broedschroed/NixieClockUltra/docs/marketing/NixieClockUltra-Werbetext.odt

Nixie Clock Ultra

wenn Zeit leuchtet

Handgefertigte Röhrenuhr · ESP32-S3 · 6 × IN-12A · WiFi & Web-Interface

# Eine Uhr, die man nicht kauft, weil man die Zeit nicht kennt

Nixie-Röhren gehören zu den faszinierendsten Anzeigetechnologien, die je entwickelt wurden: warmes, leicht diffuses Licht, das Ziffern plastisch aus dem Glas herausleuchten lässt — unverwechselbar, zeitlos und heute begehrter denn je. Die Nixie Clock Ultra bringt dieses Feeling ins 21. Jahrhundert, ohne seinen Charakter zu verlieren.

Sechs IN-12A-Nixieröhren zeigen Stunden, Minuten und Sekunden — und auf Wunsch auch das Datum. Hinter jeder Röhre sitzt eine individuell ansteuerbare RGB-LED, die das Glas von innen in warmem Licht erstrahlen lässt: statisch, im sanften Atemrhythmus oder als fließendes Farbspektrum. Vier weitere LEDs beleuchten die Trennpunkte zwischen den Zifferngruppen.

Was diese Uhr von den meisten anderen Nixie-Projekten unterscheidet, ist die Art der Röhrenansteuerung: Kein Multiplexing, keine Kompromisse. Jede der 60 Kathoden besitzt ihren eigenen Hochvolt-Transistor — die Ziffern leuchten dauerhaft, ohne jegliches Ghosting oder Flimmern. Das Ergebnis ist ein sauberes, stabiles Bild, das man sofort sieht und lange nicht vergisst.

Die Uhr denkt mit: Ein ESP32-S3 verbindet sich mit dem Heimnetz, synchronisiert die Uhrzeit vollautomatisch per NTP aus dem Internet und ist über jeden Browser erreichbar — kein App-Download, kein Pairing. Über das Web-Interface lassen sich Helligkeit, Farben, Animationen, Nacht-Modus und vieles mehr bequem einstellen. Wer lieber zur Fernbedienung greift: fast jede handelsübliche IR-Fernbedienung lässt sich anlernen.

Für ruhige Nächte sorgt der Nacht-Modus: Die Uhr dimmt sich auf Wunsch zu einer konfigurierbaren Uhrzeit automatisch herunter — oder reagiert direkt auf die Umgebungshelligkeit über einen eingebauten Lichtsensor. Im Dunkelmodus erlöschen die Röhren vollständig.

Und weil eine Uhr auch eine Uhr sein soll: Die Echtzeituhr mit CR2032-Backup-Batterie hält die Zeit auch bei Stromausfall zuverlässig. Beim nächsten Einschalten zeigt die Nixie Clock Ultra sofort die richtige Zeit — und blendet sie mit einem sanften Fade-In ein.

Die Nixie Clock Ultra ist ein Unikat — handgefertigte Einzelplatinen, sorgfältig bestückt und getestet. Kein Bausatz, keine Kompromisse. Eine Uhr, die man nicht kauft, weil man die Uhrzeit nicht kennt — sondern weil man sie kennen will.

# Features auf einen Blick

Anzeige

- 6 × IN-12A Nixie-Röhren — direkte Kathodensteuerung ohne Multiplexing, kein Ghosting, kein Flimmern
- Stunden · Minuten · Sekunden sowie Datumsanzeige (TT MM JJ)
- Sanfter Fade-In beim Einschalten
- Optional weicher Ziffernwechsel (Crossfade) — einzeln zuschaltbar für Sekundentakt und für den Wechsel zwischen Uhrzeit und Datum

Beleuchtung

- 6 × WS2812B RGB-LEDs als Röhrenhintergrundbeleuchtung (individuell pro Röhre)
- 4 × WS2812B RGB-LEDs für die Trennpunkt-Beleuchtung
- Animationsmodi: Rainbow, Statisch (warmweiß), Puls
- Slot-Machine-Effekt: konfigurierbar (aus / alle 10 s / 1 min / 15 min / 1 h), zeigt danach automatisch das Datum
- Rollgeschwindigkeit der Slot-Machine-Animation stufenlos einstellbar

Konnektivität & Bedienung

- ESP32-S3 mit integriertem WLAN (2,4 GHz)
- Gleichzeitig eigener WLAN-Accesspoint (kein Heimnetz notwendig) und WLAN-Client
- Automatische Zeitsynchronisation per NTP
- Vollständiges Web-Interface im Browser — kein App-Download, funktioniert auf Smartphone, Tablet und PC
- Erreichbar per IP oder als nixieclockcs.local im Heimnetz (mDNS)
- IR-Fernbedienung: 8 Funktionen frei auf jede handelsübliche Fernbedienung anlernbar
- 4 Bedientaster direkt an der Uhr

Nacht-Modus

- Zeitgesteuertes Dimmen oder vollständiges Ausschalten der Röhren
- Automatische Helligkeitsanpassung über eingebauten Lichtsensor (LDR)
- NeoPixel-Helligkeit wird im Nacht-Modus proportional mitgedimmt

Technik

- Zweiplatinen-Design: Logic Board (ESP32-S3, RTC, Spannungsversorgung) + Nixie Display Board
- DS1302 Echtzeituhr mit CR2032-Batterie-Backup — hält Zeit auch ohne Strom
- Hochvolt-Versorgung: 5 V USB → DC-DC-Konverter → 10 V → HV-Modul → ~170 V stabile Anodenspannung
- 60 diskrete SMBTA42-Hochvolt-Transistoren (je eine Kathode, je eine Röhrenziffer)
- Alle Einstellungen werden im Flash gespeichert und bleiben nach Stromunterbrechung erhalten
- Stromversorgung: Micro-USB, 5 V

Nixie Clock Ultra · A. Schröder · 2026
