broedschroed/NixieClockUltra/docs/superpowers/specs/2026-07-12-website-i18n-toggle-design.md

# Design-Spec: Website – Sprachumschalter Deutsch/Englisch

**Datum:** 2026-07-12
**Status:** Genehmigt, bereit zur Implementierung

---

## Ziel

Die bestehende statische Projektwebseite (`docs/website/`, 6 Seiten, siehe
`2026-06-29-projektwebseite-design.md`) bekommt einen client-seitigen Sprachumschalter
Deutsch/Englisch. Umschalten erfolgt ohne Seiten-Reload und ohne URL-Wechsel, die Wahl
bleibt über Seitennavigation hinweg erhalten. Kein Build-Schritt — der GitHub-Pages-Workflow
lädt `docs/website` weiterhin unverändert 1:1 hoch.

Geltungsbereich: alle 6 Seiten (`index`, `features`, `aufbau`, `geschichte`,
`dokumentation`, `galerie`).

---

## Architektur & neue/geänderte Dateien

**Neu:**
- `js/i18n-de.js` — Wörterbuch, ein `key: "deutscher Text"`-Eintrag pro übersetzbarem
  Textbaustein, gruppiert nach Seite plus globale `nav.*`/`footer.*`-Keys
- `js/i18n-en.js` — gleiche Keys, englische Übersetzungen (von mir übersetzt, analog zum
  bereits vorhandenen englischen README)
- `js/i18n.js` — Kernlogik: Sprache ermitteln, Wörterbuch anwenden, Umschalter-Klicks
  behandeln

**Geändert:**
- Alle 6 HTML-Seiten: übersetzbare Textknoten bekommen `data-i18n="key"`-Attribute;
  deutscher Text bleibt als sichtbarer Fallback-Inhalt im HTML stehen (progressive
  enhancement — ohne JS bleibt die Seite auf Deutsch lesbar)
- `js/nav.js`: rendert den DE/EN-Umschalter rechts in der Nav-Leiste (`.nav-inner`,
  analog zum bestehenden `.nav-toggle`/`.nav-inner a.active`-Muster); ruft nach dem
  Injizieren von Header/Nav/Footer `applyLanguage()` aus `i18n.js` auf, damit auch die
  injizierten Footer-Texte übersetzt werden
- `css/style.css`: Styling für `.lang-switch` (DE│EN-Umschalter), passend zum
  bestehenden Nav-Look

**Reihenfolge beim Seitenaufbau:** `nav.js` injiziert Header/Nav/Footer →
`i18n.js` wendet die gespeicherte Sprache auf das gesamte Dokument an (inkl. der
gerade injizierten Teile). Beide Skripte laufen bei `DOMContentLoaded`.

---
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
