broedschroed/NixieClockUltra/docs/website/img/gallery/01 Die Uhr von hinten.jpg

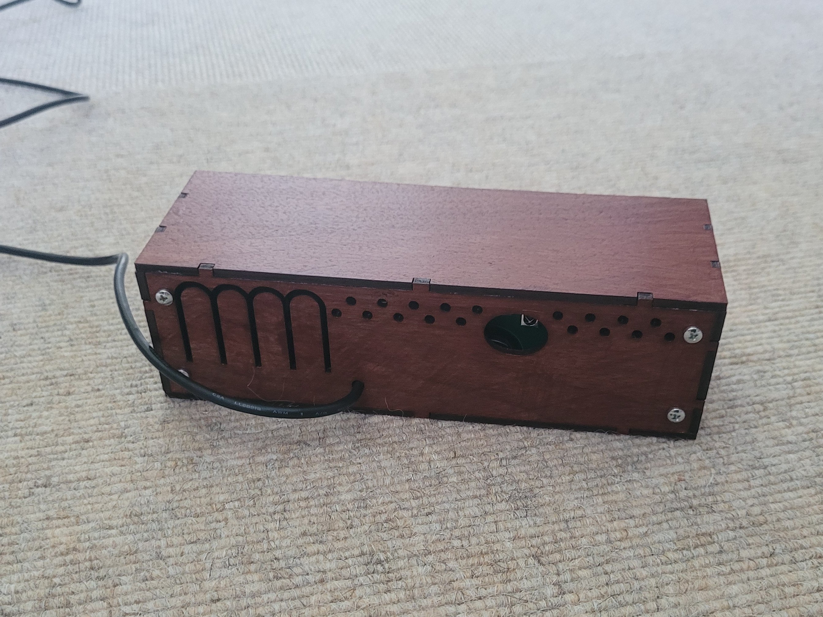
docs/website/img/gallery/01 Die Uhr von hinten.jpg
