broedschroed/NixieClockUltra/docs/website/img/gallery/01 Einsatzbeispiel 1.png

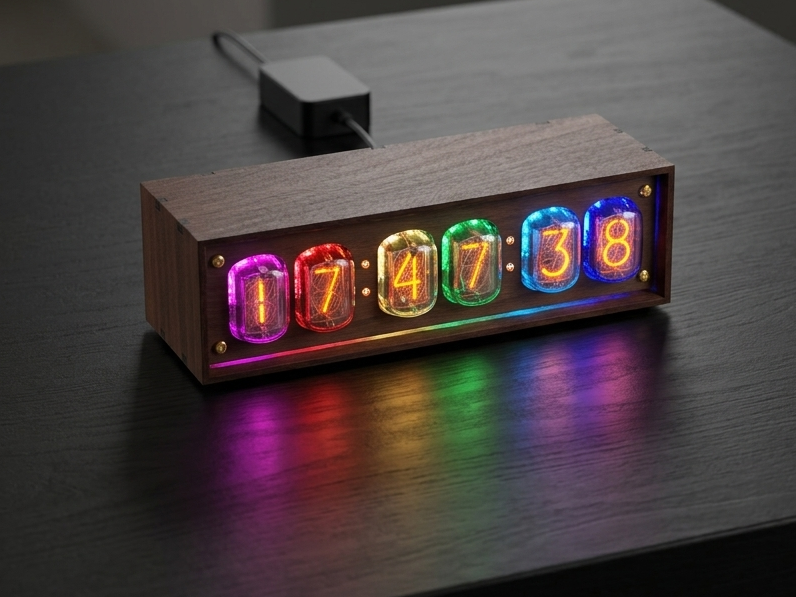
docs/website/img/gallery/01 Einsatzbeispiel 1.png
