broedschroed/NixieClockUltra/docs/website/img/gallery/01 Einsatzbeispiel 2.png

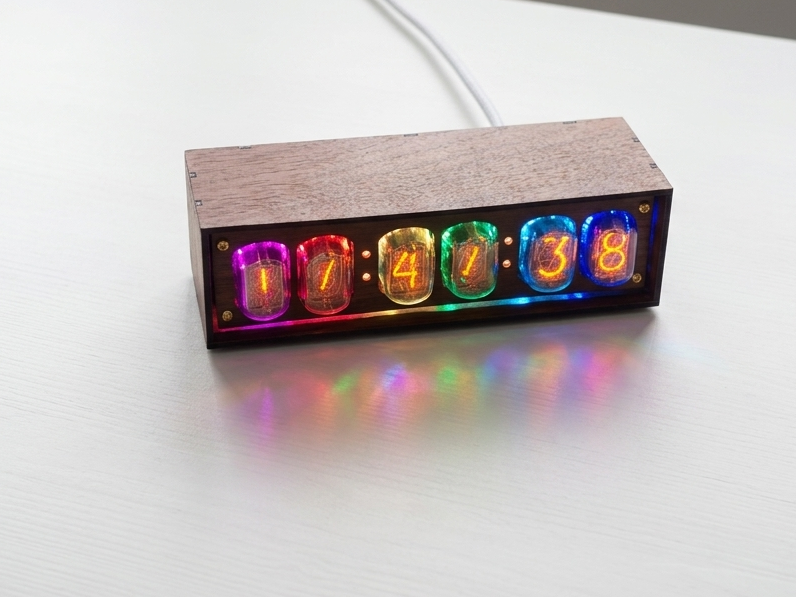
docs/website/img/gallery/01 Einsatzbeispiel 2.png
