broedschroed/NixieClockUltra/docs/website/img/gallery/01 Uhr im Betrieb 2.jpg

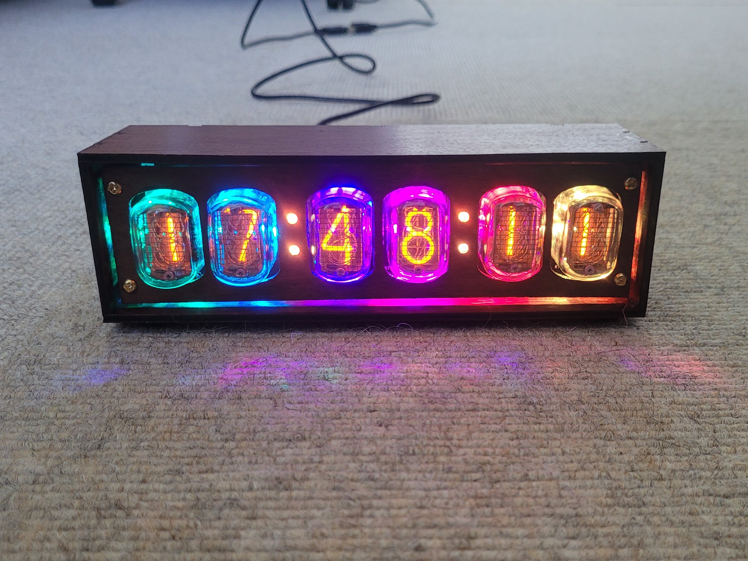
docs/website/img/gallery/01 Uhr im Betrieb 2.jpg
