broedschroed/NixieClockUltra/docs/website/img/gallery/01 Uhr im Betrieb.jpg

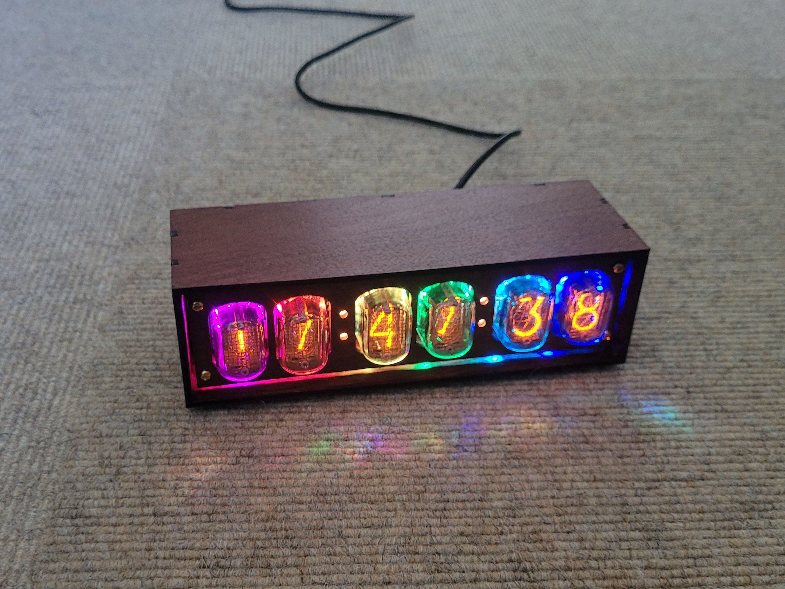
docs/website/img/gallery/01 Uhr im Betrieb.jpg
