broedschroed/NixieClockUltra/docs/website/img/gallery/01 Uhr linke Seite.jpg

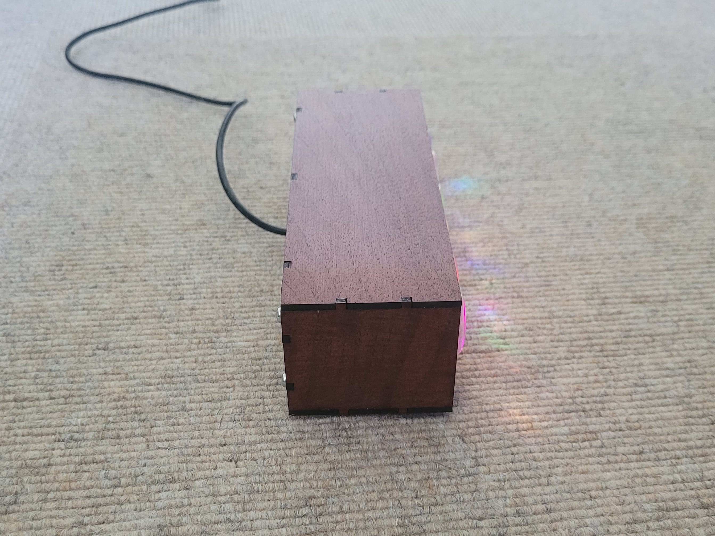
docs/website/img/gallery/01 Uhr linke Seite.jpg
