broedschroed/NixieClockUltra/docs/website/img/gallery/01 Uhr mit Web-UI und Fernbedienung.jpg

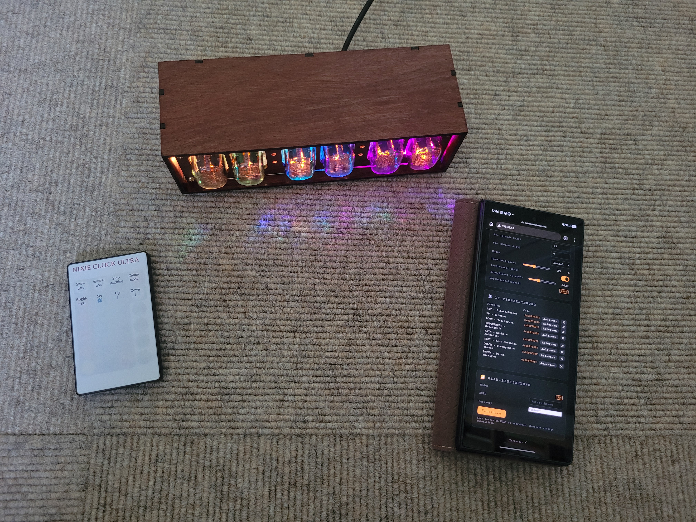
docs/website/img/gallery/01 Uhr mit Web-UI und Fernbedienung.jpg
