broedschroed/NixieClockUltra/docs/website/img/gallery/01 Uhr rechte Seite.jpg

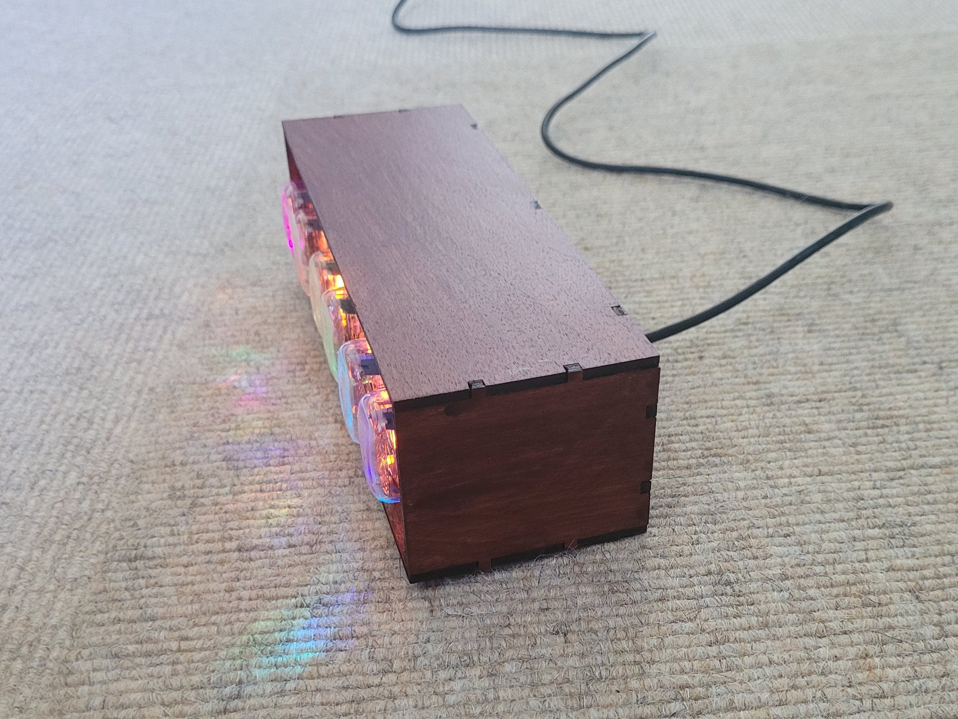
docs/website/img/gallery/01 Uhr rechte Seite.jpg
