broedschroed/NixieClockUltra/docs/website/img/gallery/01 Uhr von unten.jpg

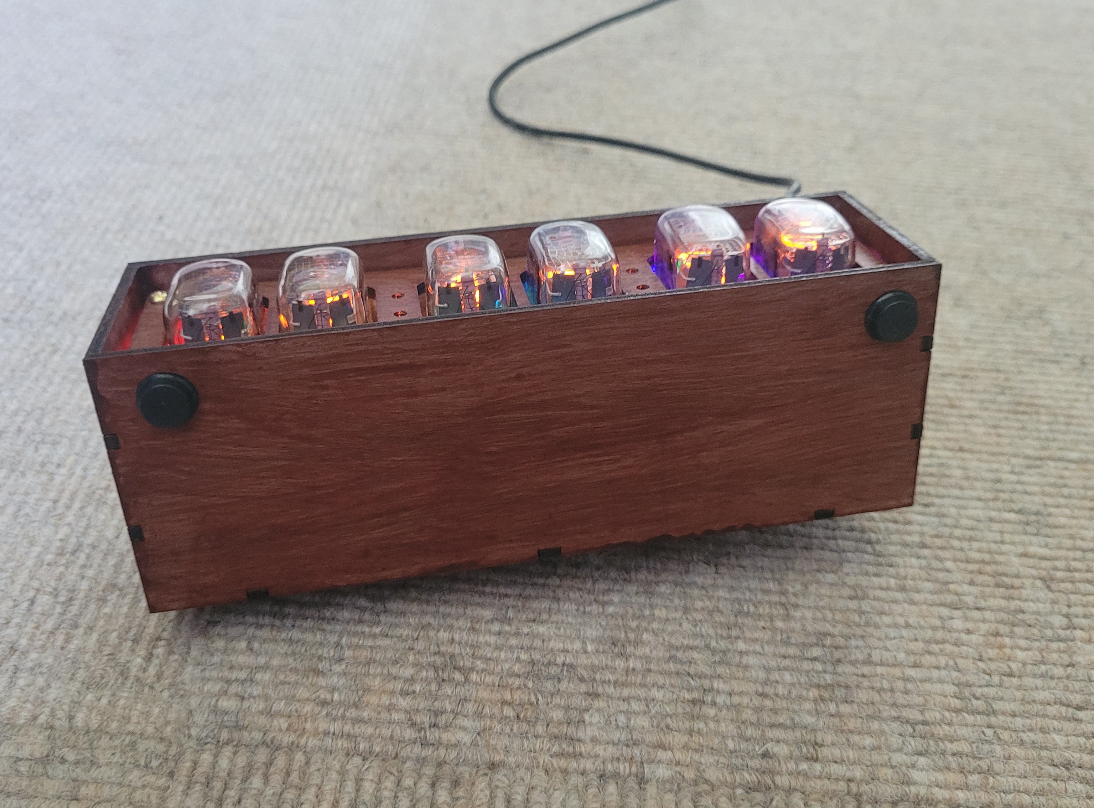
docs/website/img/gallery/01 Uhr von unten.jpg
