broedschroed/NixieClockUltra/docs/website/img/gallery/01WebUI1.png

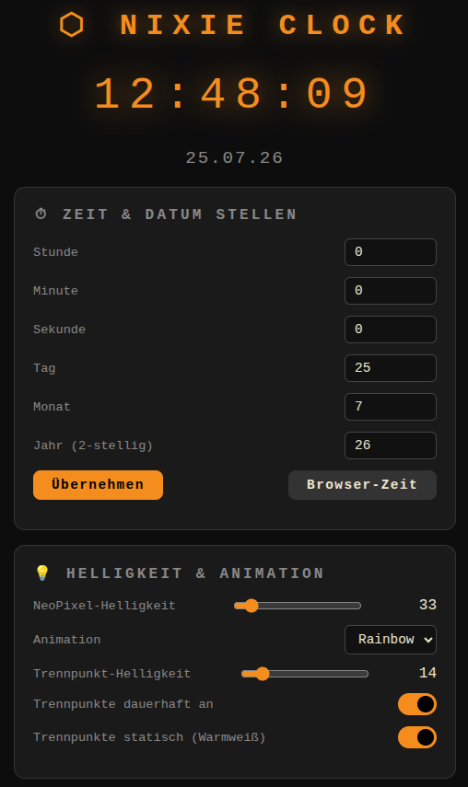
docs/website/img/gallery/01WebUI1.png
