broedschroed/NixieClockUltra/docs/website/img/gallery/01WebUI2.png

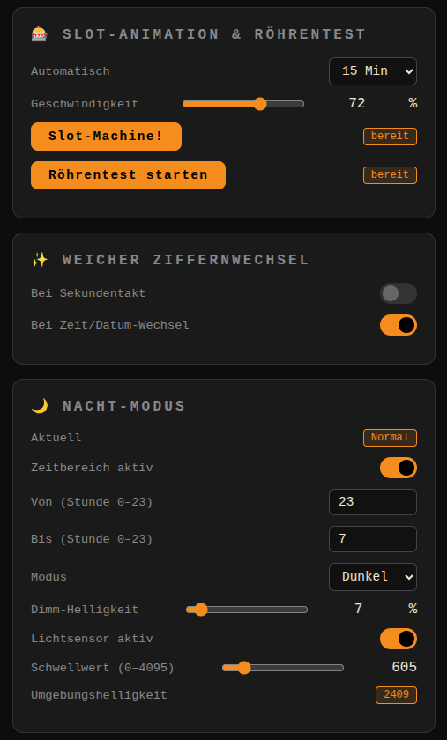
docs/website/img/gallery/01WebUI2.png
