broedschroed/NixieClockUltra/docs/website/img/gallery/01WebUI3.png

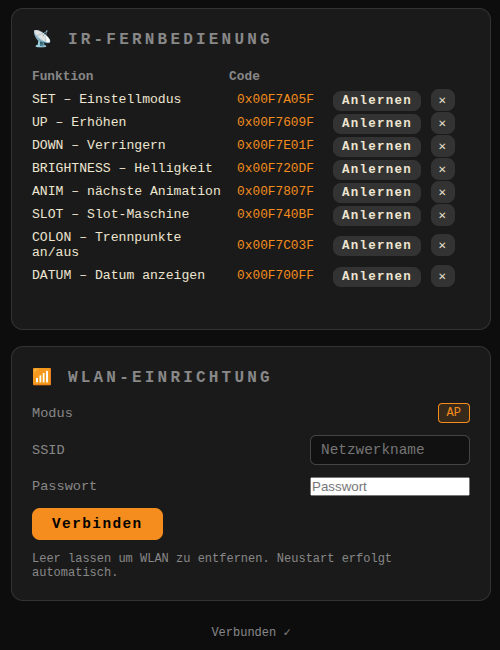
docs/website/img/gallery/01WebUI3.png
