broedschroed/NixieClockUltra/docs/website/img/gallery/02 Karton mit unbenutzten Röhren 1.jpg

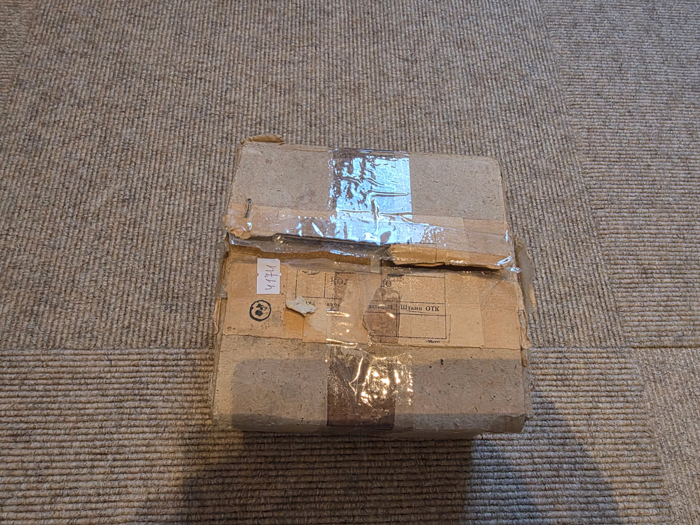
docs/website/img/gallery/02 Karton mit unbenutzten Röhren 1.jpg
