broedschroed/NixieClockUltra/docs/website/img/gallery/02 Karton mit unbenutzten Röhren 2.jpg

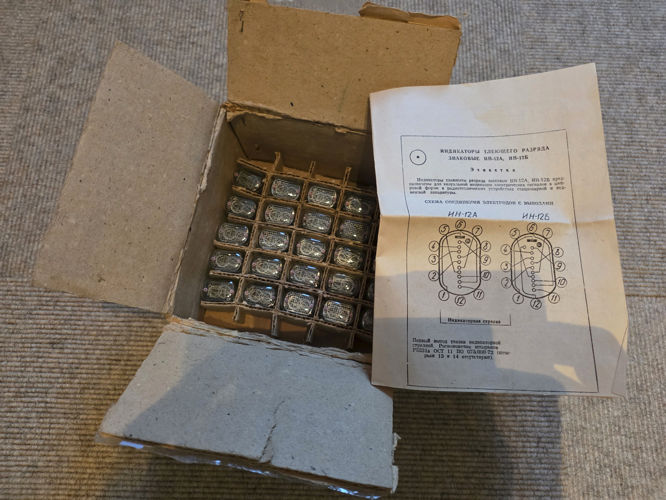
docs/website/img/gallery/02 Karton mit unbenutzten Röhren 2.jpg
