broedschroed/NixieClockUltra/docs/website/img/gallery/02 zusammengebaut.jpg

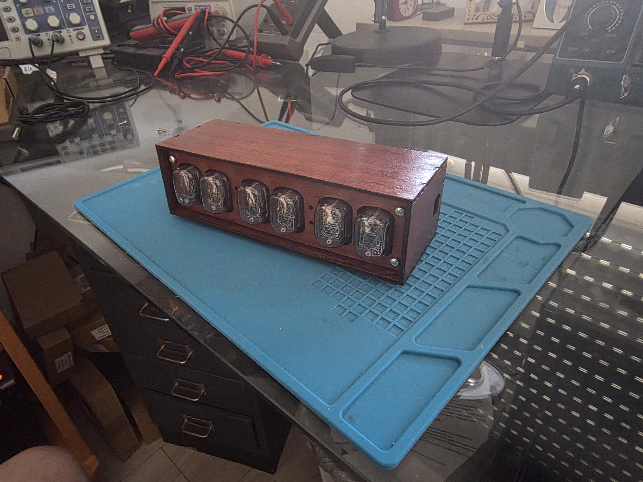
docs/website/img/gallery/02 zusammengebaut.jpg
