broedschroed/NixieClockUltra/docs/website/img/gallery/05 Essigwasser reduziert den Geruch.jpg

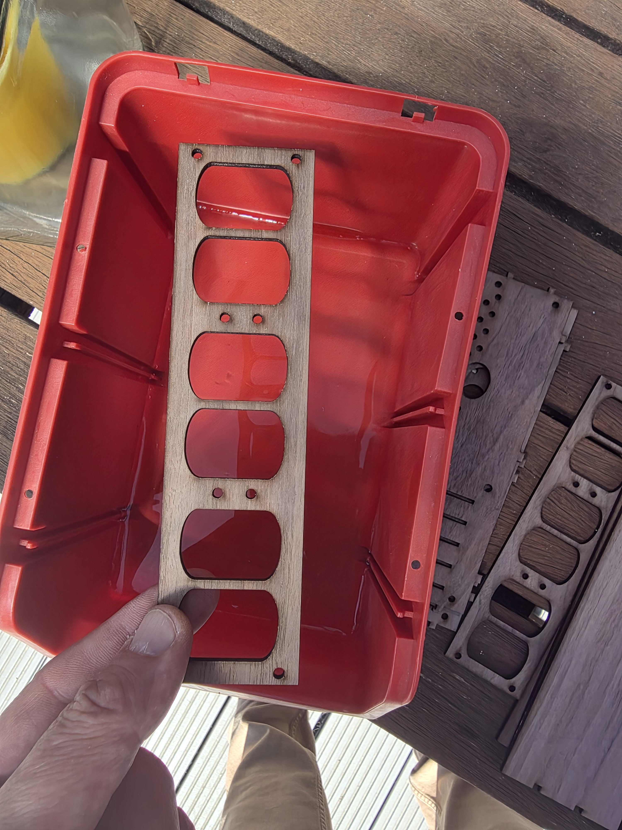
docs/website/img/gallery/05 Essigwasser reduziert den Geruch.jpg
