broedschroed/NixieClockUltra/docs/website/img/gallery/06 Badetag beendet.jpg

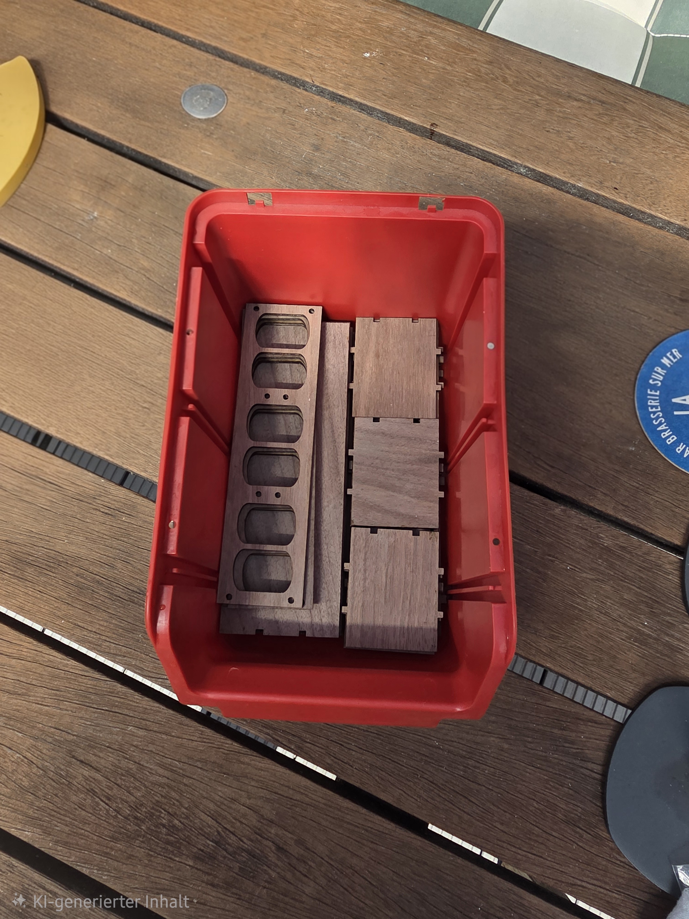
docs/website/img/gallery/06 Badetag beendet.jpg
