broedschroed/NixieClockUltra/docs/website/img/gallery/06 frisch gelasertes Gehäuse.jpg

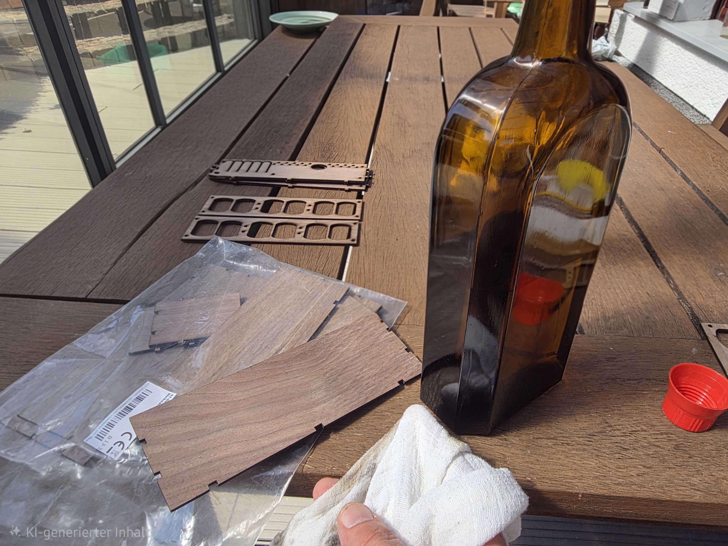
docs/website/img/gallery/06 frisch gelasertes Gehäuse.jpg
