broedschroed/NixieClockUltra/docs/website/img/gallery/07 Gehäuseteile einer Uhr.jpg

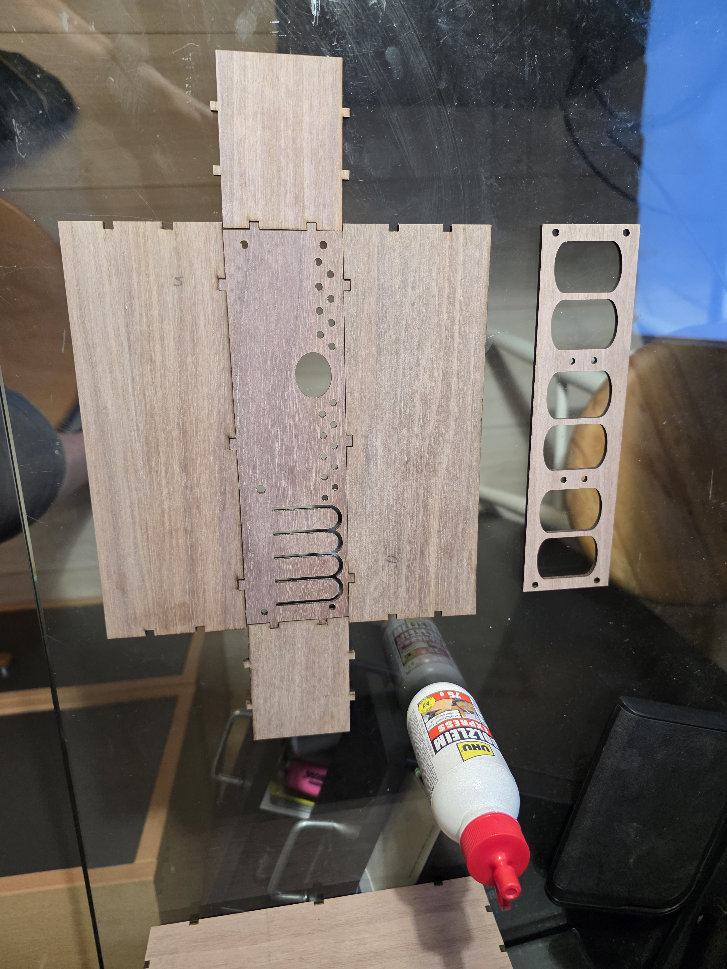
docs/website/img/gallery/07 Gehäuseteile einer Uhr.jpg
