broedschroed/NixieClockUltra/docs/website/img/gallery/08 Dank Noppen einfach verleimt.jpg

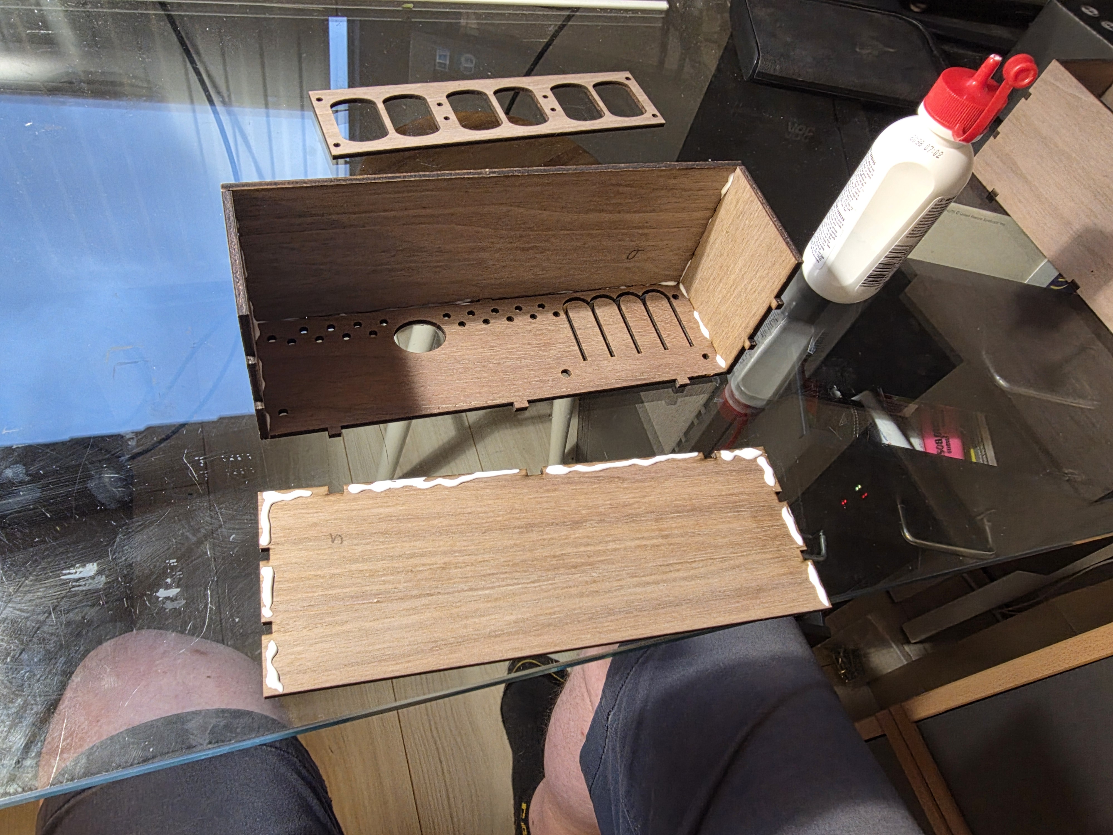
docs/website/img/gallery/08 Dank Noppen einfach verleimt.jpg
