broedschroed/NixieClockUltra/docs/website/img/gallery/11 IN-12-Platine von unten - eine Menge Transistoren.jpg

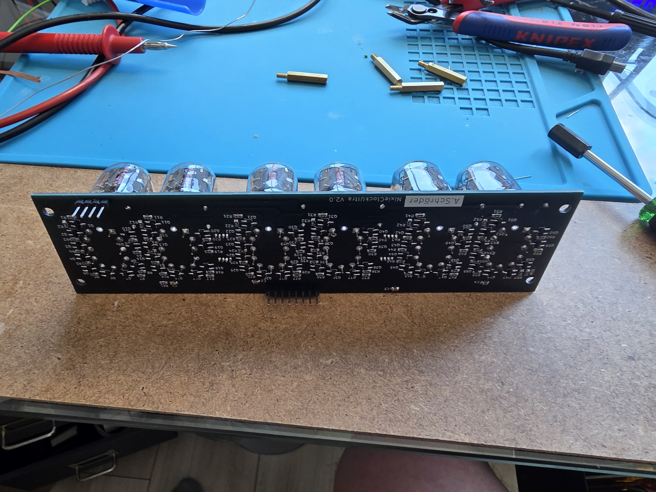
docs/website/img/gallery/11 IN-12-Platine von unten - eine Menge Transistoren.jpg
