broedschroed/NixieClockUltra/docs/website/img/gallery/12 IN-12-Platine von oben.jpg

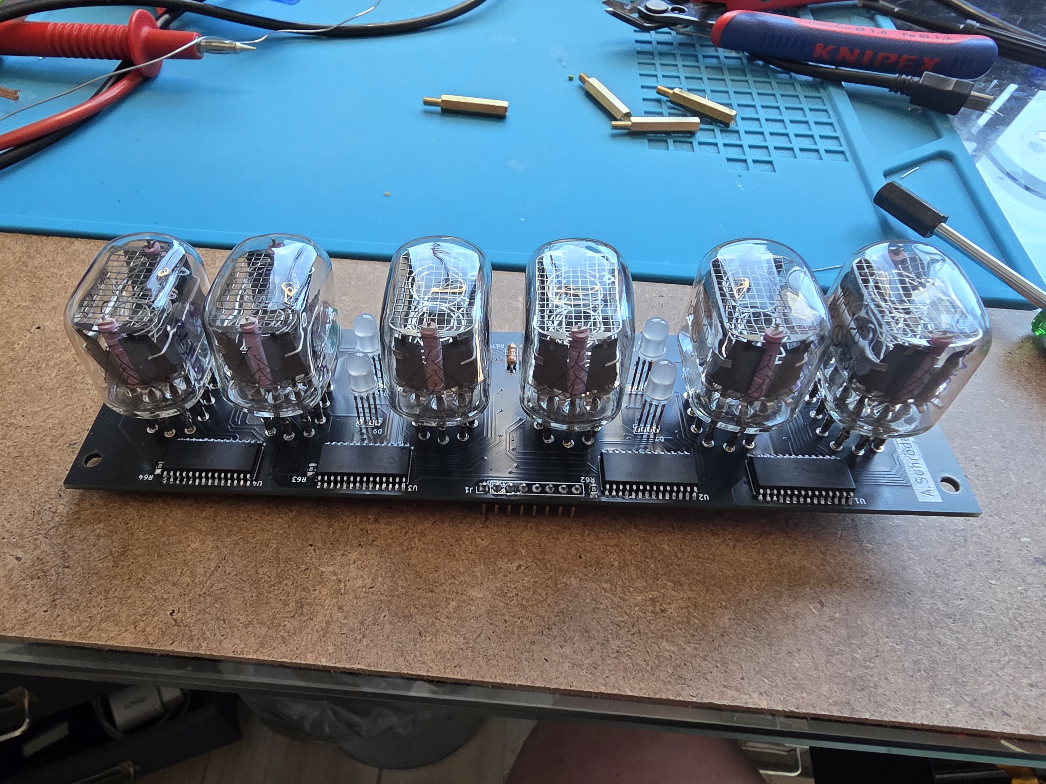
docs/website/img/gallery/12 IN-12-Platine von oben.jpg
