broedschroed/NixieClockUltra/docs/website/img/gallery/13 Logicboard von oben.jpg

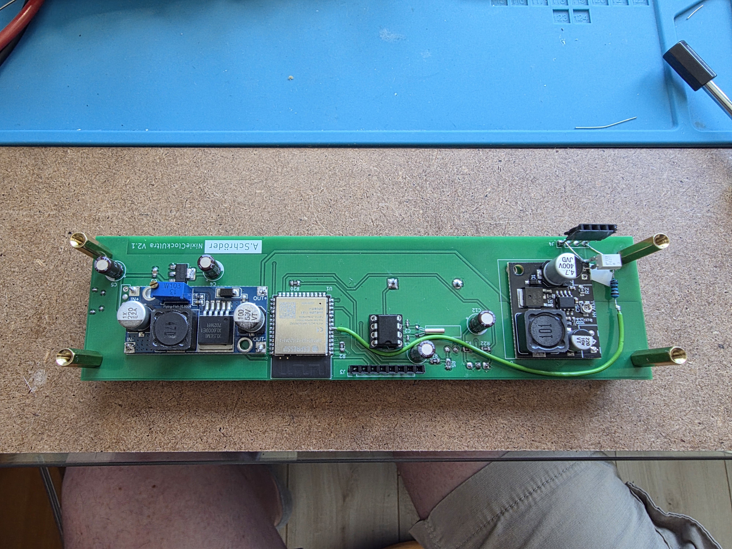
docs/website/img/gallery/13 Logicboard von oben.jpg
