broedschroed/NixieClockUltra/docs/website/img/gallery/14 Logicboard von unten.jpg

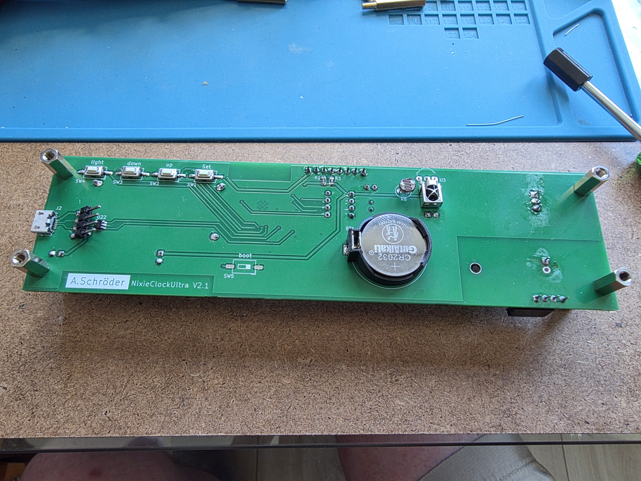
docs/website/img/gallery/14 Logicboard von unten.jpg
