broedschroed/NixieClockUltra/docs/website/img/gallery/17 Füße für Taster-Bedienung.jpg

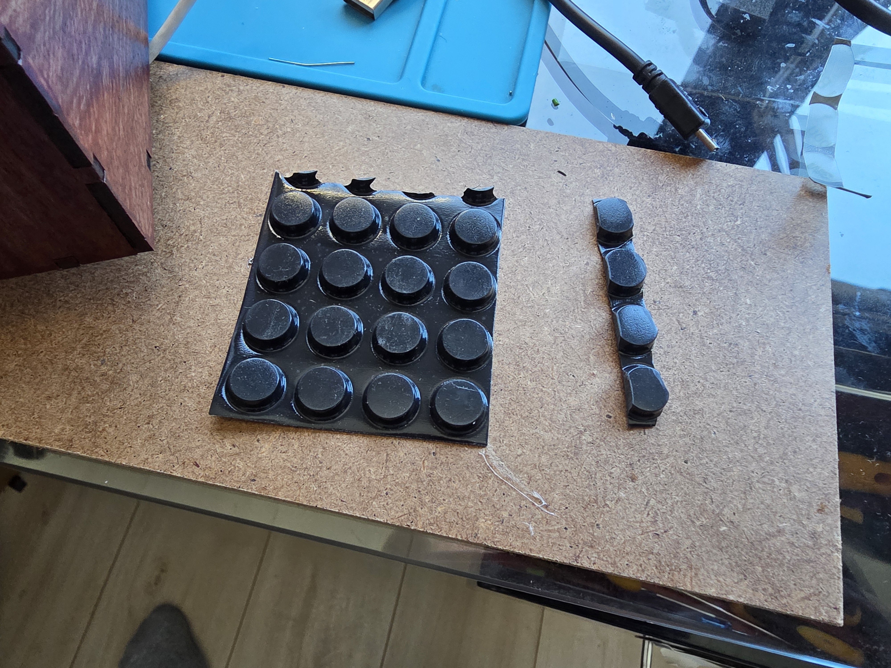
docs/website/img/gallery/17 Füße für Taster-Bedienung.jpg
