broedschroed/NixieClockUltra/docs/website/img/gallery/18 Füße für Taster-Bedienung 2.jpg

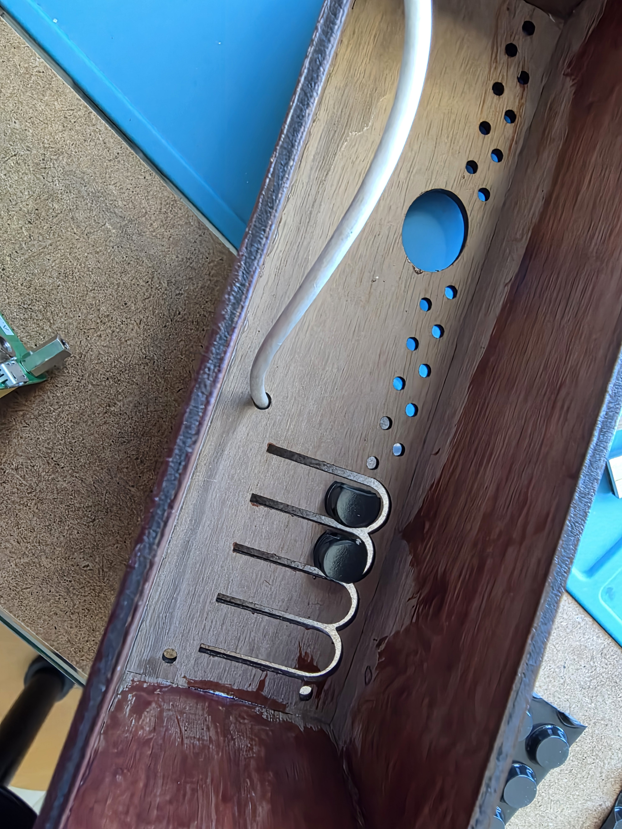
docs/website/img/gallery/18 Füße für Taster-Bedienung 2.jpg
