broedschroed/NixieClockUltra/docs/website/img/gallery/19 Gehäuseversion Kabel hinten.jpg

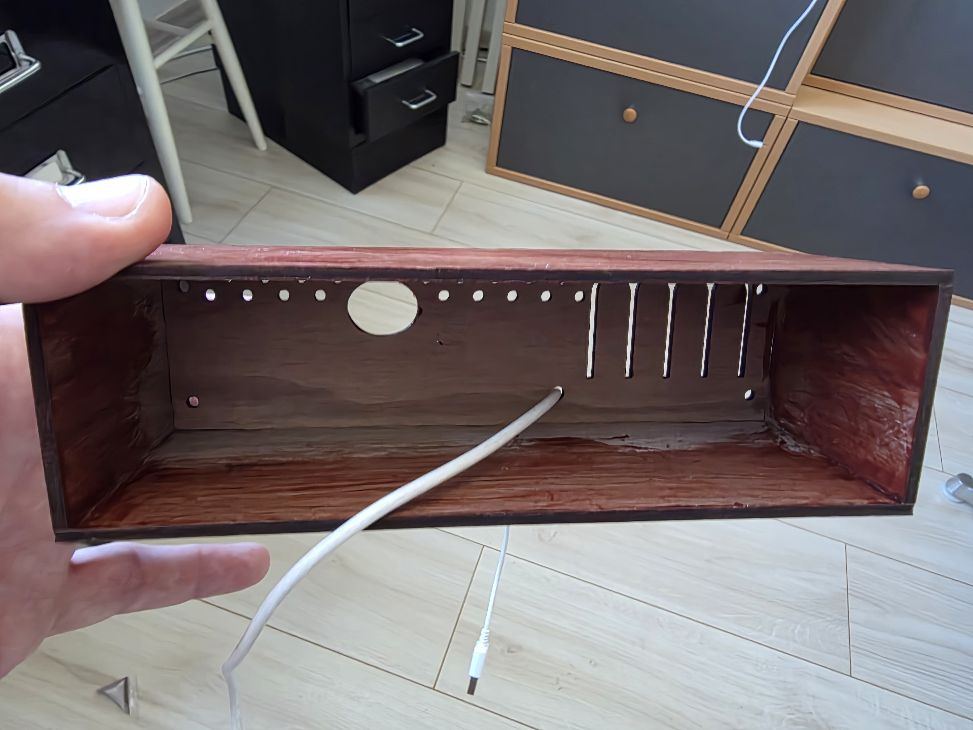
docs/website/img/gallery/19 Gehäuseversion Kabel hinten.jpg
