broedschroed/NixieClockUltra/docs/website/img/gallery/23 Fertig.jpg

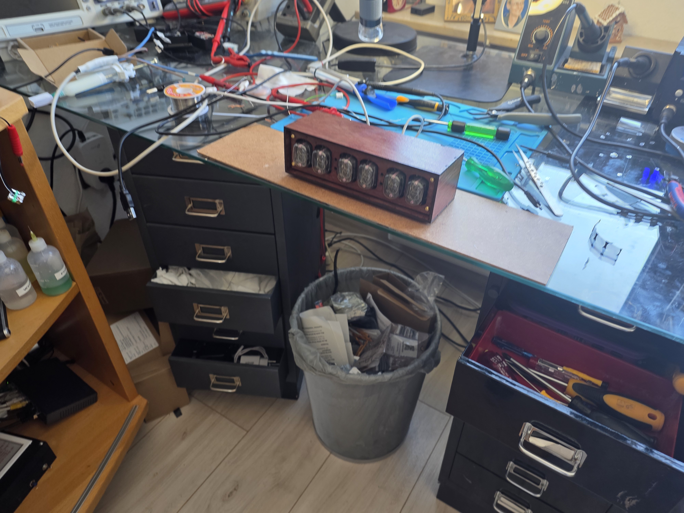
docs/website/img/gallery/23 Fertig.jpg
