broedschroed/NixieClockUltra/docs/website/img/gallery/24 Uhr-Generationen.jpg

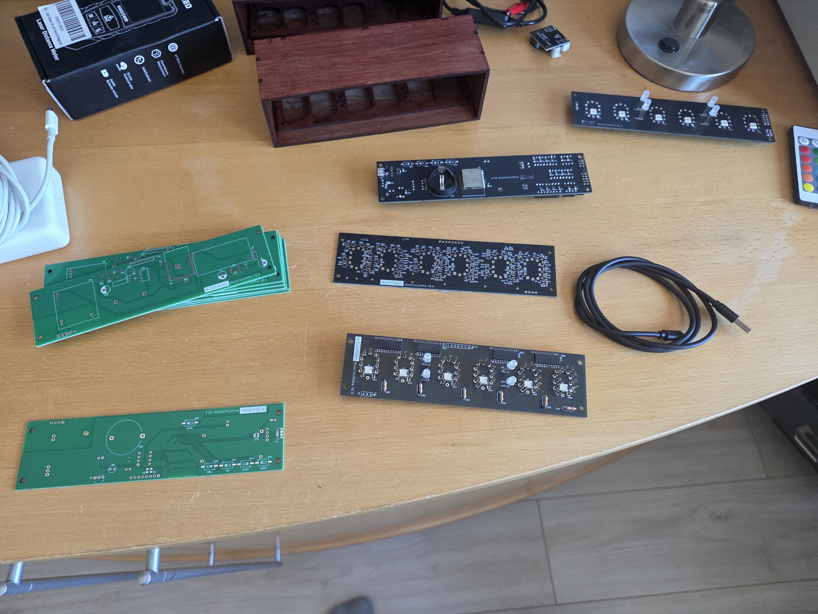
docs/website/img/gallery/24 Uhr-Generationen.jpg
