broedschroed/NixieClockUltra/docs/website/img/hero.jpg

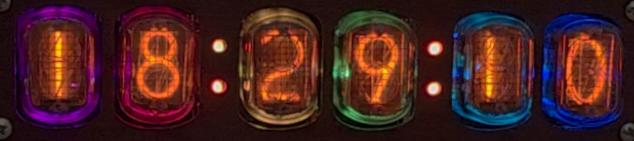
docs/website/img/hero.jpg
