broedschroed/NixieClockUltra/docs/website/img/Teaser.png

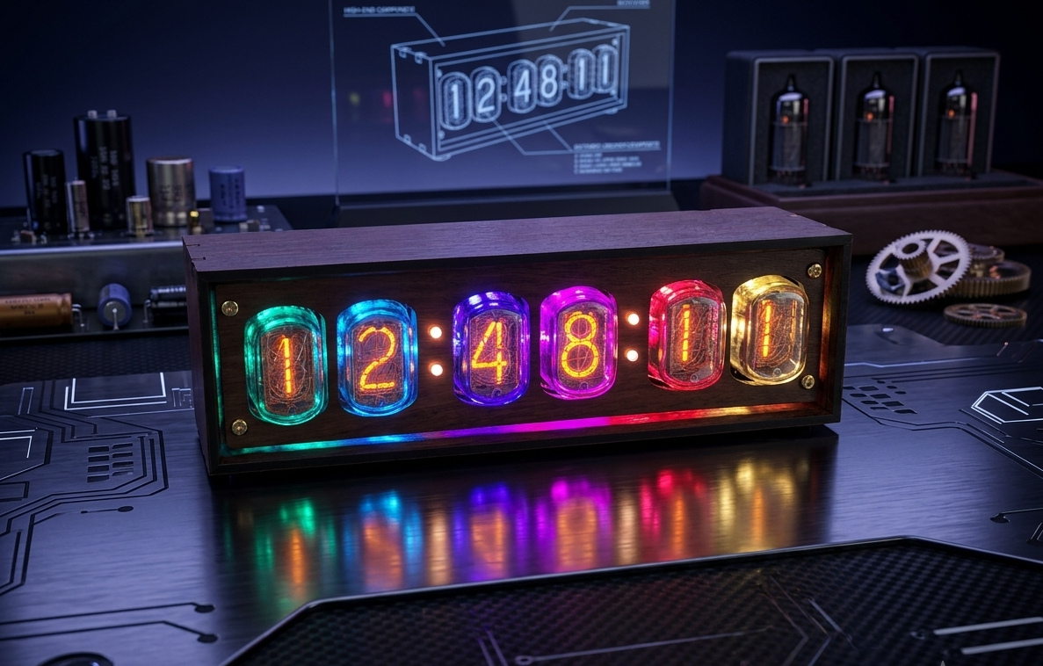
docs/website/img/Teaser.png
