broedschroed/NixieClockUltra/docs/Leiterplatten/Logic-Board/nixieclocklogic_V2-2-SCH.pdf

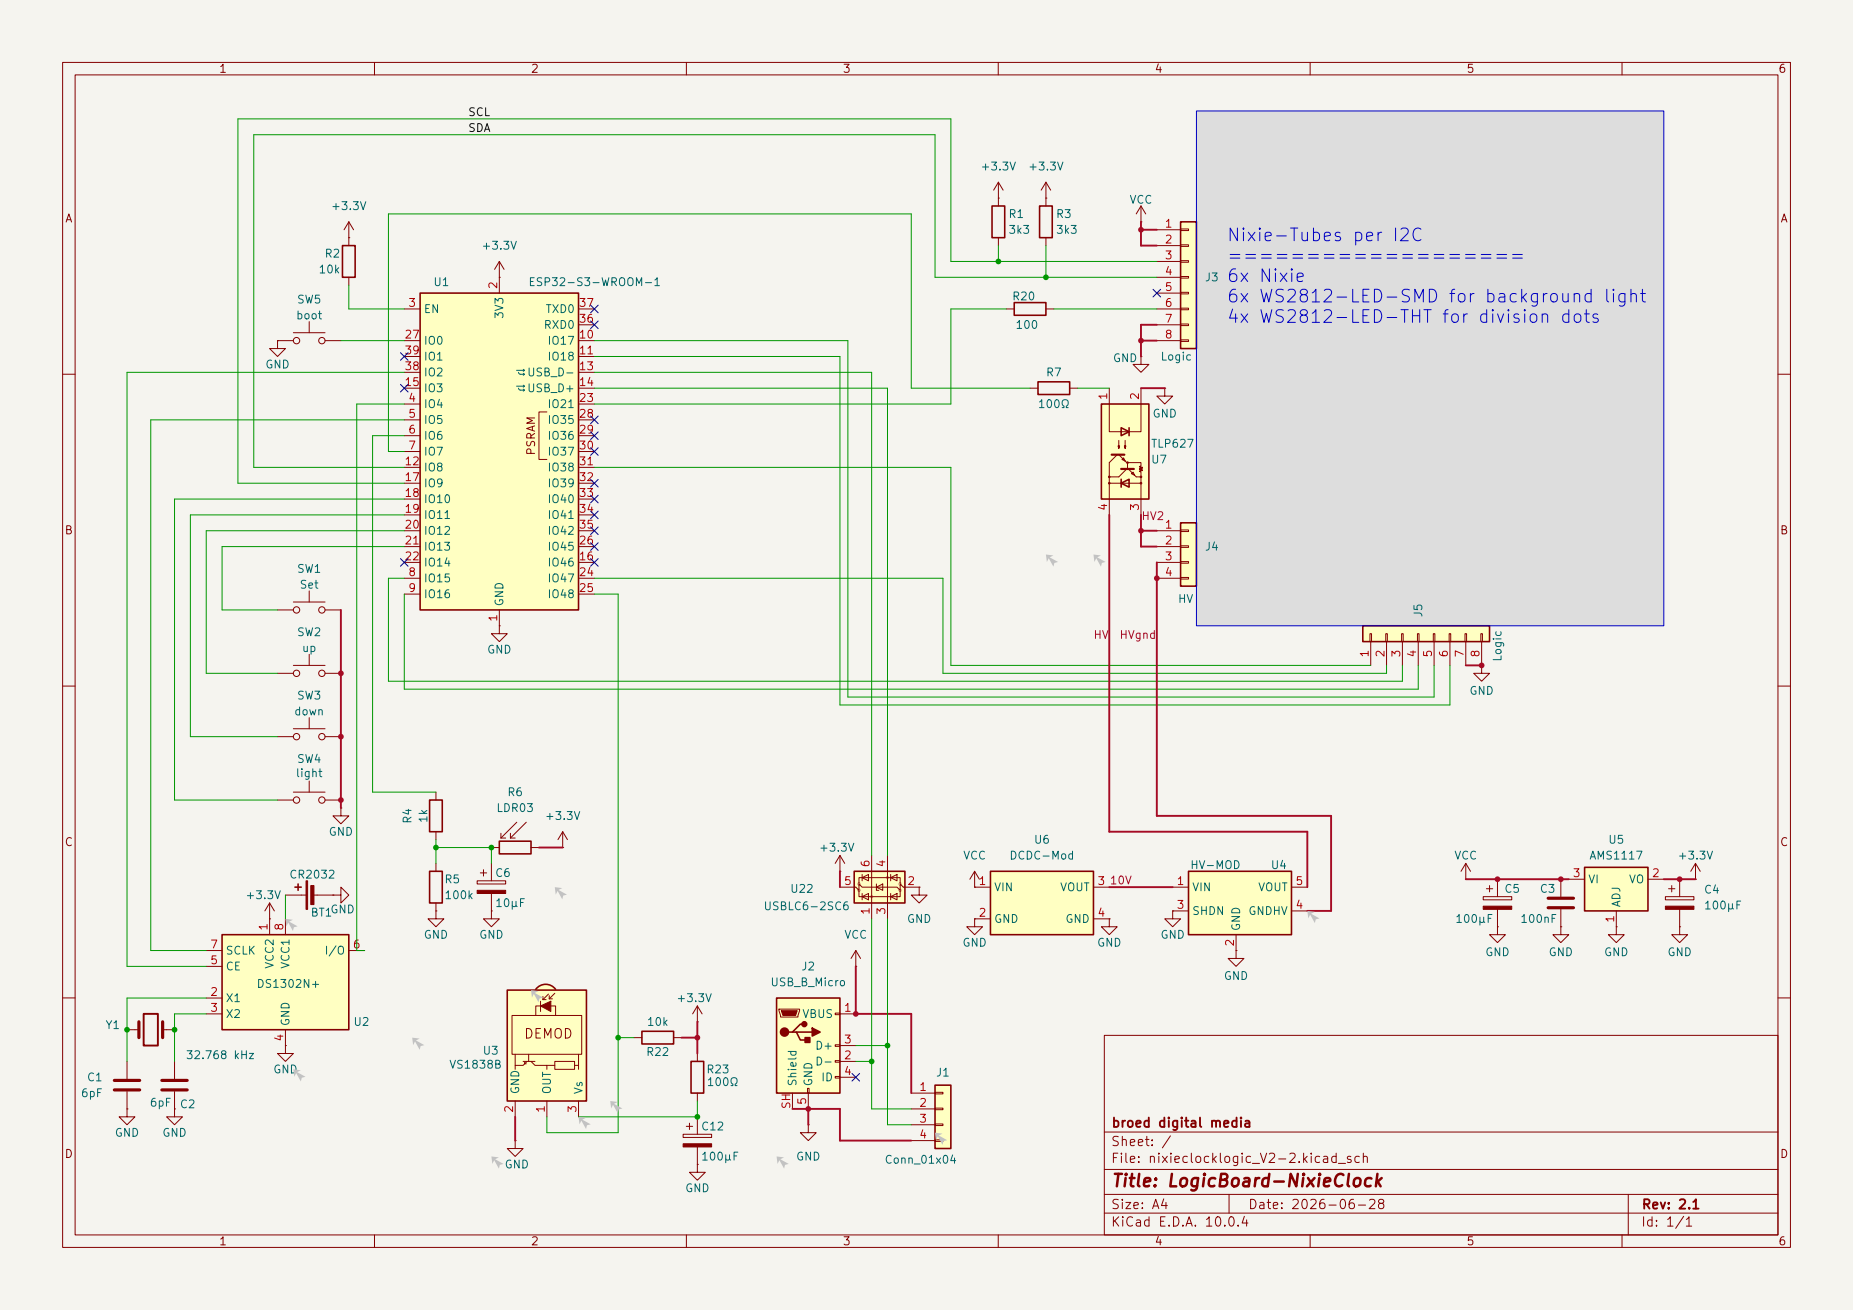
[picture p59: page 1]
