broedschroed/NixieClockUltra/docs/website/img/gallery/09 zum Aushärten fixiert.jpg

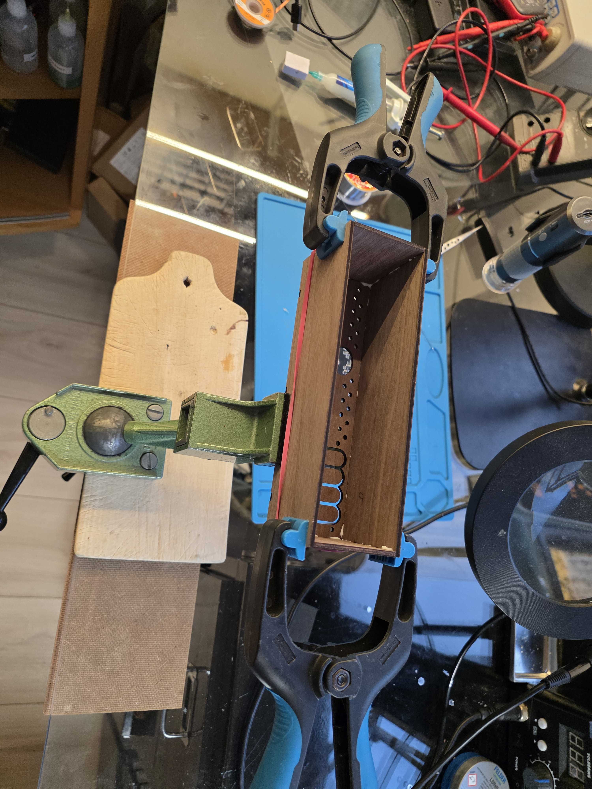
docs/website/img/gallery/09 zum Aushärten fixiert.jpg
