broedschroed/NixieClockUltra/docs/website/img/gallery/20 Gehäuse von hinten.jpg

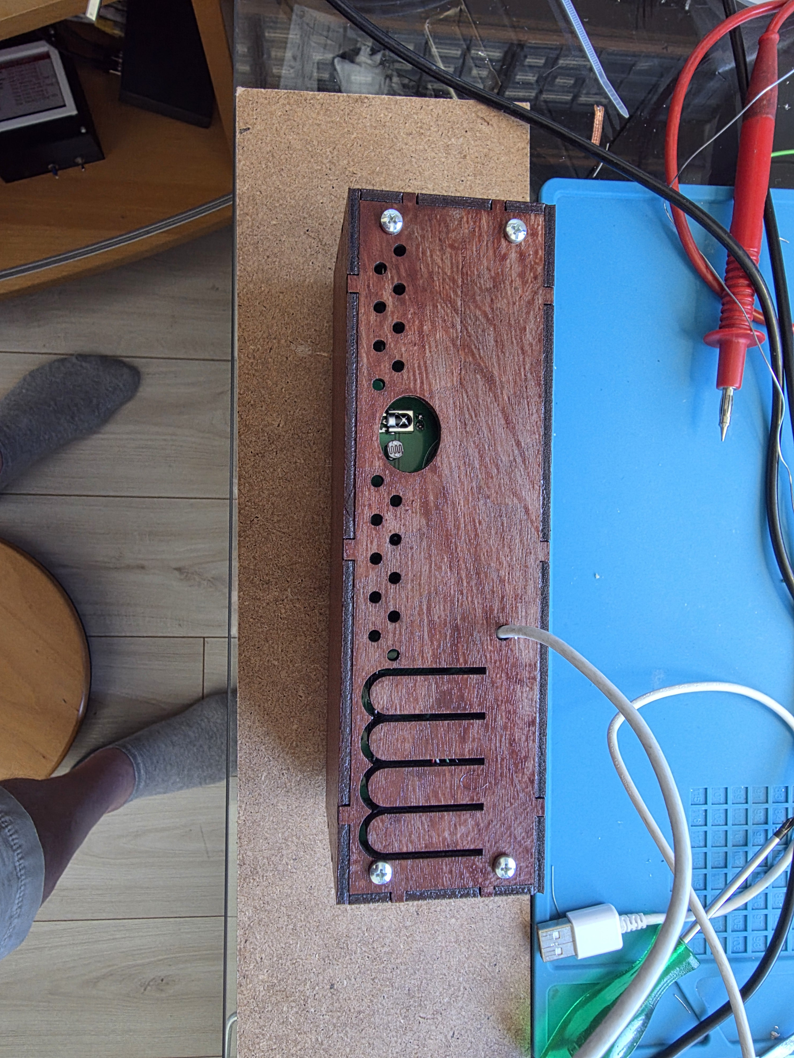
docs/website/img/gallery/20 Gehäuse von hinten.jpg
