broedschroed/NixieClockUltra/docs/website/img/gallery/22 Gehäuse von unten.jpg

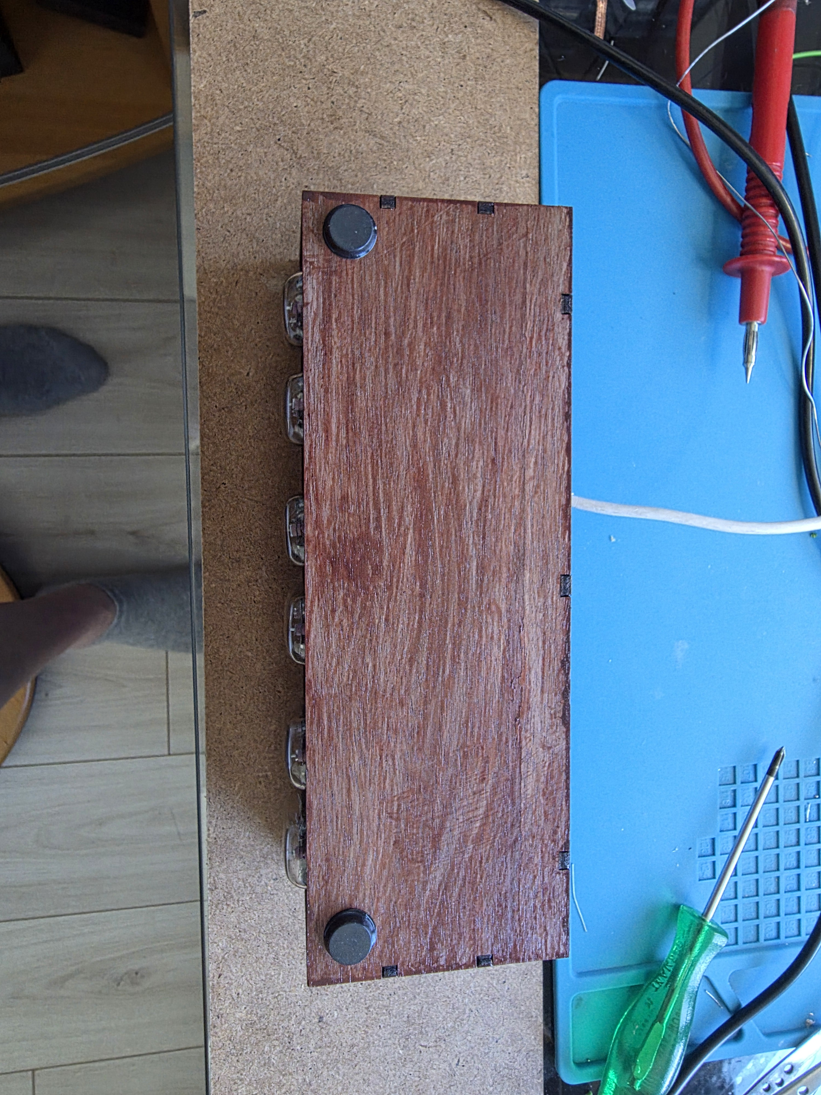
docs/website/img/gallery/22 Gehäuse von unten.jpg
